oldgerman/mR-71-RE/AD_Project/MR-71_RE0/Images/PCB_统计.png

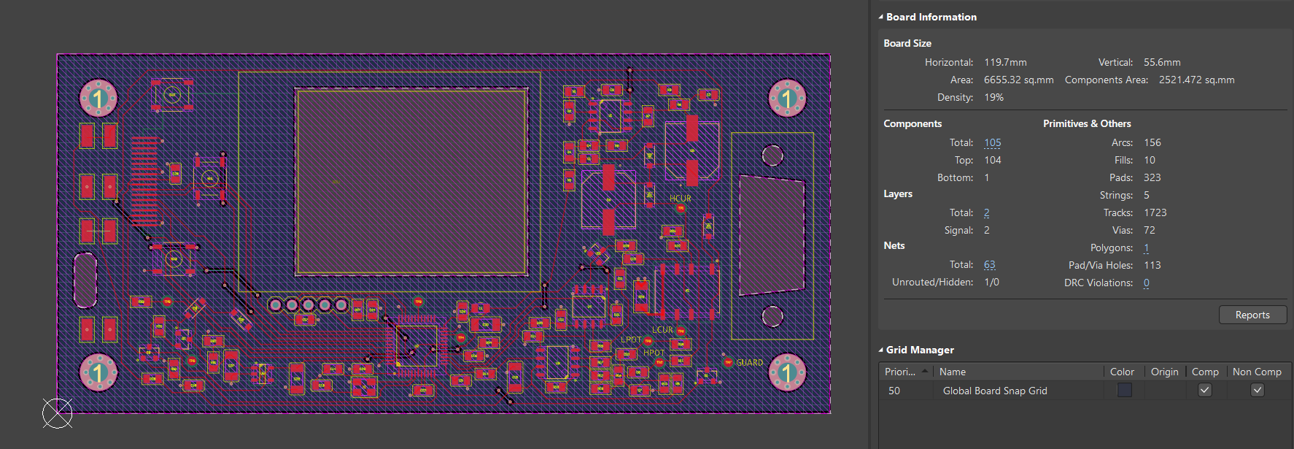
AD_Project/MR-71_RE0/Images/PCB_统计.png
