oldgerman/mR-71-RE/Gerber/mR-71-RE/20240321-1013_MR-71_RE6_Gold：HQDFM计算沉金面积是18.5%.png

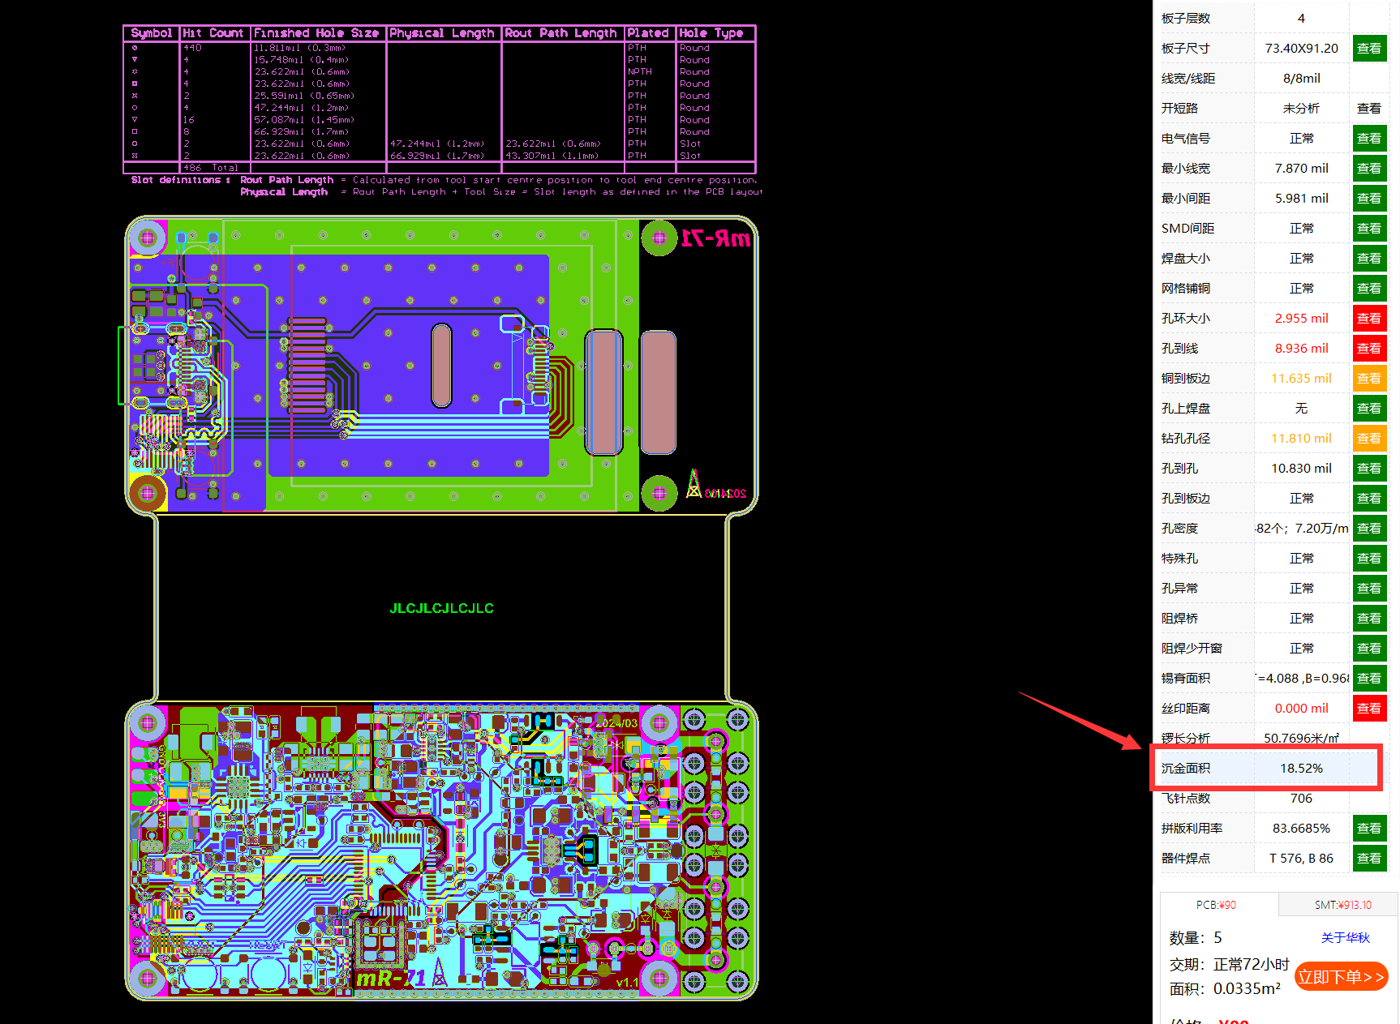
Gerber/mR-71-RE/20240321-1013_MR-71_RE6_Gold：HQDFM计算沉金面积是18.5%.png
