oldgerman/mR-71-RE/Gerber/mR-71_RE_Stencil/20240319_mR-71_RE6_Stencil_10x10cm.png

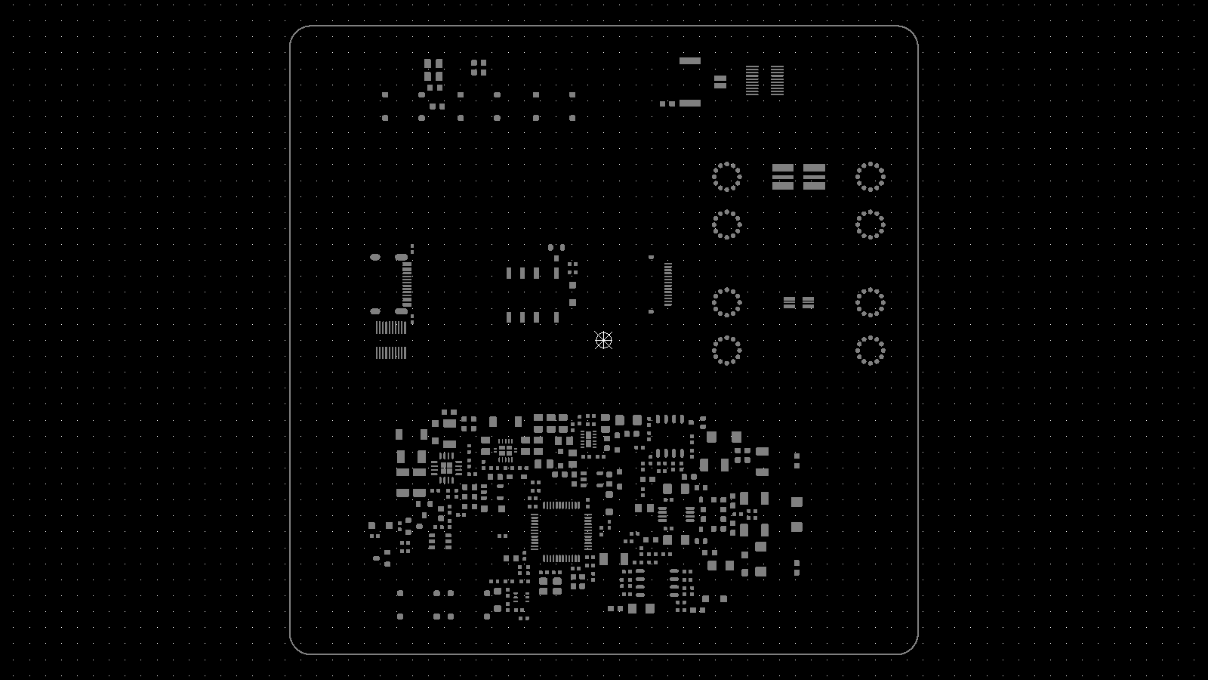
Gerber/mR-71_RE_Stencil/20240319_mR-71_RE6_Stencil_10x10cm.png
