oldgerman/mR-71-RE/Images/mR-71-RE6：1号2号机成品图：2.jpg

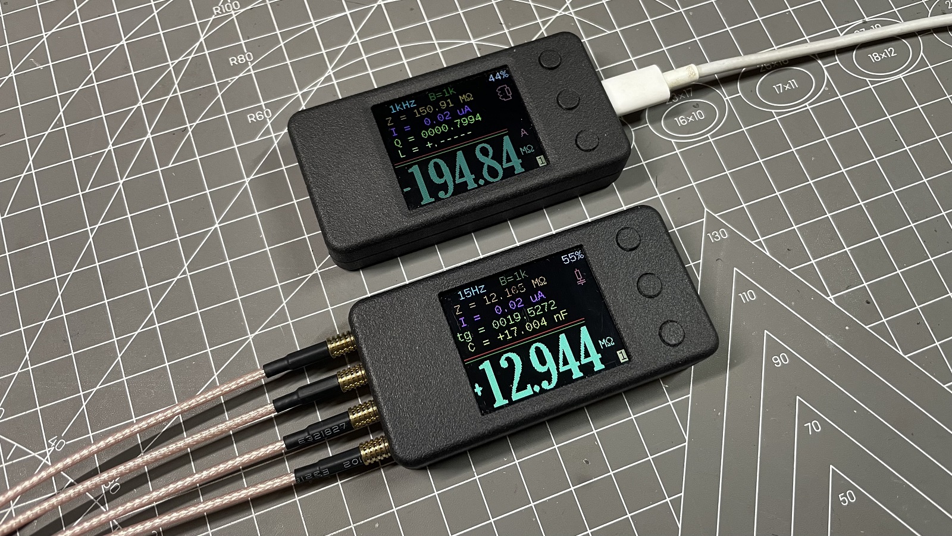
Images/mR-71-RE6：1号2号机成品图：2.jpg
