oldgerman/mR-71-RE/Images/mR-71-RE6：初号机成品图：1.jpg

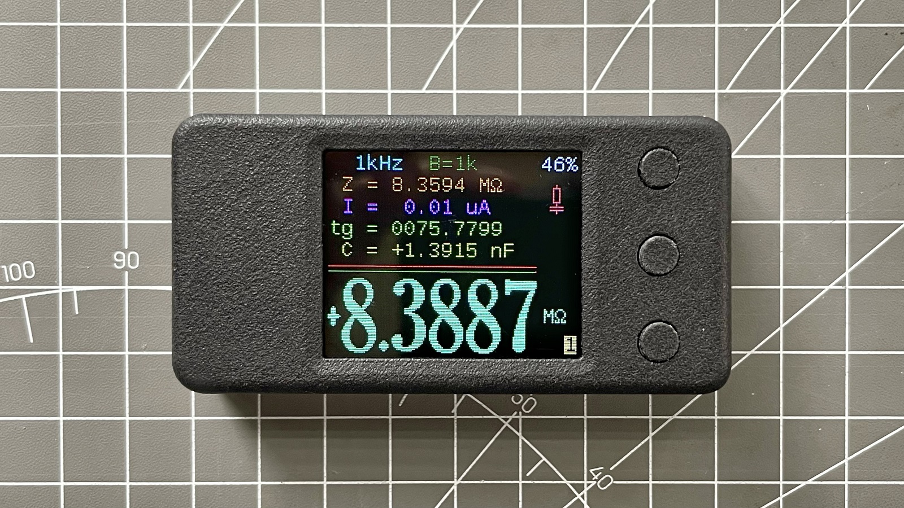
Images/mR-71-RE6：初号机成品图：1.jpg
