oldgerman/mR-71-RE/Images/mR-71-RE6：外壳处理完成的效果.JPG

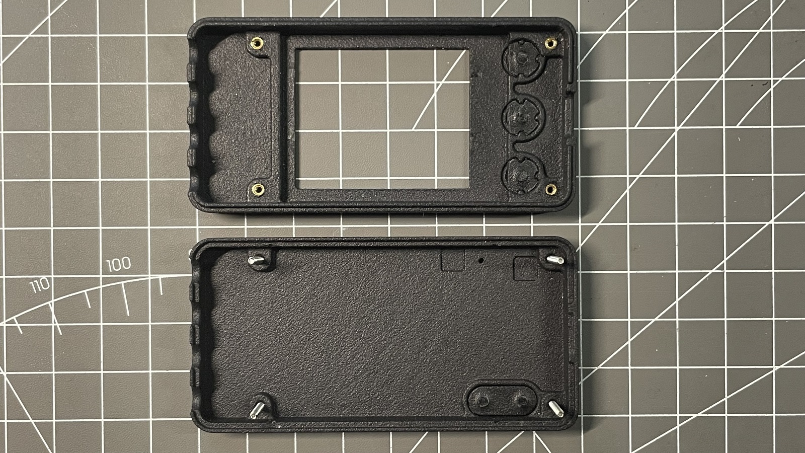
Images/mR-71-RE6：外壳处理完成的效果.JPG
