oldgerman/mR-71-RE/Images/mR-71-RE：v1.0_PCB：1.JPG

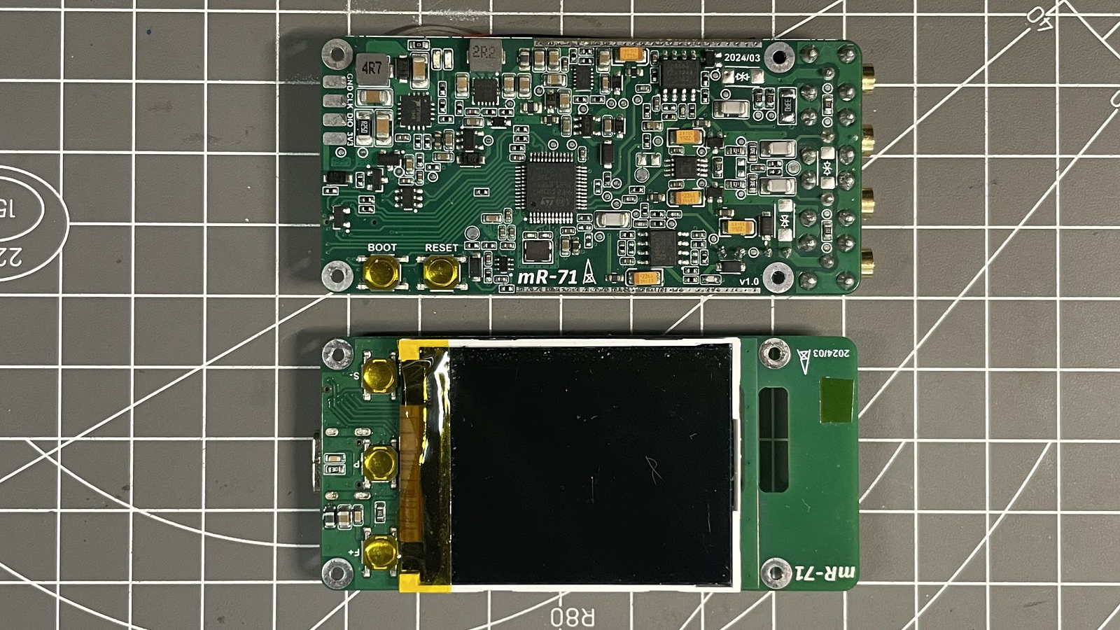
Images/mR-71-RE：v1.0_PCB：1.JPG
